pgreendale/RiceRework/2-Simulation/Preamp_HiGain.asc

C1: cap; 10n; Rser=882.6m Lser=318.58p
C2: cap; 10n; Rser=786.2m Lser=151.38p
C3: cap; 10µ; Rser=27.8m Lser=187.57p
C4: cap; 10µ; Rser=16.5m Lser=200.49p
C5: cap; 470p; Rser=16.5m Lser=200.49p
J1: njf; SST113
J2: njf; J113
J3: njf; J310
R1: res; 6.8k
R2: res; 6.8k
R3: res; {Rc}
R4: res; {Rbias}
R5: res; {Rbias}
R6: res; {Rbias}
R7: res; {Rbias}
R8: res; 150
R9: res; {Rin}
R10: res; {Rin}
V1: voltage; 48; Rser=0
Vcommon: voltage; ""; AC .5 0
Vsig1: voltage; ""; AC .5 0; Rser=0
Vsig2: voltage; ""; AC .5 0; Rser=0
Named nets: 0, VCC, Out1, Out2, V_in-, V_in+
.ac dec 10 10 100k
.param Rin=6.8k Rbias=3.3Meg Rc=3.3k
.step param Rcurrent 500 4.7k 100
